mwuerms/lighthouse_hardware/scad/lighthouse/display.scad

/**
 * Martin Egli
 * 2024-05-15
 * testing honey comb structure to create the display
 * wall thickness: 0.5 mm
 * printing: 0.2 mm layer height
 */

use <hexagonparts.scad>
use <m3screw.scad>

hex_rad = 8/2;
/* calculate hexagon center positions
 * r: radius, use "hex_rad"
 * n: index in x axis
 * m: index in y axis
 * even columns
 * dxeven = n*2*r*cos(30)
 * dyeven = m*3/2*r
 * odd columns
 * dxodd = n*3/2*r
 * dyodd = (m-1/2)*r*cos(30)
 */
dx_even_factor = 3/2*hex_rad; // see dxeven = m*3*r
dy_even_factor = 2*hex_rad*cos(30); // see dyeven = n*2*r*cos(30)
dx_odd_factor = 3/2*hex_rad; // see dxodd = m*3/2*r
dy_odd_factor = hex_rad*cos(30); // see dyodd = (2n+1)*r*cos(30)

module display_m3_mount_cut() {
    place_m3_mount_cut(0, 2);
    place_m3_mount_cut(5, -2);
    place_m3_mount_cut(5, 6);
    place_m3_mount_cut(10, 5);
    place_m3_mount_cut(13, -2);
    place_m3_mount_cut(15, 6);
    place_m3_mount_cut(20, 4);
}

// - plain display ------------------
module plain_display_cover() {
    place_hexagon_cover_element(0, 0);
    place_hexagon_cover_element(0, 1);
    *place_hexagon_cover_element(0, 2);
    
    place_hexagon_cover_element(1, -1);
    place_hexagon_cover_element(1, 0);
    place_hexagon_cover_element(1, 1);
    place_hexagon_cover_element(1, 2);
    place_hexagon_cover_element(1, 3);
    place_hexagon_cover_element(1, 4);
    place_hexagon_cover_element(1, 5);

    place_hexagon_cover_element(2, -1);
    place_hexagon_cover_element(2, 0);
    place_hexagon_cover_element(2, 1);
    place_hexagon_cover_element(2, 2);
    place_hexagon_cover_element(2, 3);
    place_hexagon_cover_element(2, 4);
    place_hexagon_cover_element(2, 5);

    place_hexagon_cover_element(3, -1);
    place_hexagon_cover_element(3, 0);
    place_hexagon_cover_element(3, 1);
    place_hexagon_cover_element(3, 2);
    place_hexagon_cover_element(3, 3);
    place_hexagon_cover_element(3, 4);
    place_hexagon_cover_element(3, 5);
    place_hexagon_cover_element(3, 6);

    place_hexagon_cover_element(4, -2);
    place_hexagon_cover_element(4, -1);
    place_hexagon_cover_element(4, 0);
    place_hexagon_cover_element(4, 1);
    place_hexagon_cover_element(4, 2);
    place_hexagon_cover_element(4, 3);
    place_hexagon_cover_element(4, 4);
    place_hexagon_cover_element(4, 5);

    *place_hexagon_cover_element(5, -2);
    place_hexagon_cover_element(5, -1);
    place_hexagon_cover_element(5, 0);
    place_hexagon_cover_element(5, 1);
    place_hexagon_cover_element(5, 2);
    place_hexagon_cover_element(5, 3);
    place_hexagon_cover_element(5, 4);
    place_hexagon_cover_element(5, 5);

    place_hexagon_cover_element(6, -2);
    place_hexagon_cover_element(6, -1);
    place_hexagon_cover_element(6, 0);
    place_hexagon_cover_element(6, 1);
    place_hexagon_cover_element(6, 2);
    place_hexagon_cover_element(6, 3);
    place_hexagon_cover_element(6, 4);
    place_hexagon_cover_element(6, 5);

    place_hexagon_cover_element(7, -1);
    place_hexagon_cover_element(7, 0);
    place_hexagon_cover_element(7, 1);
    place_hexagon_cover_element(7, 2);
    place_hexagon_cover_element(7, 3);
    place_hexagon_cover_element(7, 4);
    place_hexagon_cover_element(7, 5);
    place_hexagon_cover_element(7, 6);

    place_hexagon_cover_element(8, -2);
    place_hexagon_cover_element(8, -1);
    place_hexagon_cover_element(8, 0);
    place_hexagon_cover_element(8, 1);
    place_hexagon_cover_element(8, 2);
    place_hexagon_cover_element(8, 3);
    place_hexagon_cover_element(8, 4);
    place_hexagon_cover_element(8, 5);

    place_hexagon_cover_element(9, -2);
    place_hexagon_cover_element(9, -1);
    place_hexagon_cover_element(9, 0);
    place_hexagon_cover_element(9, 1);
    place_hexagon_cover_element(9, 2);
    place_hexagon_cover_element(9, 3);
    place_hexagon_cover_element(9, 4);
    place_hexagon_cover_element(9, 5);

    place_hexagon_cover_element(10, -2);
    place_hexagon_cover_element(10, -1);
    place_hexagon_cover_element(10, 0);
    place_hexagon_cover_element(10, 1);
    place_hexagon_cover_element(10, 2);
    place_hexagon_cover_element(10, 3);
    place_hexagon_cover_element(10, 4);
    *place_hexagon_cover_element(10, 5);

    place_hexagon_cover_element(11, -1);
    place_hexagon_cover_element(11, 0);
    place_hexagon_cover_element(11, 1);
    place_hexagon_cover_element(11, 2);
    place_hexagon_cover_element(11, 3);
    place_hexagon_cover_element(11, 4);
    place_hexagon_cover_element(11, 5);

    place_hexagon_cover_element(12, -2);
    place_hexagon_cover_element(12, -1);
    place_hexagon_cover_element(12, 0);
    place_hexagon_cover_element(12, 1);
    place_hexagon_cover_element(12, 2);
    place_hexagon_cover_element(12, 3);
    place_hexagon_cover_element(12, 4);
    place_hexagon_cover_element(12, 5);

    *place_hexagon_cover_element(13, -2);
    place_hexagon_cover_element(13, -1);
    place_hexagon_cover_element(13, 0);
    place_hexagon_cover_element(13, 1);
    place_hexagon_cover_element(13, 2);
    place_hexagon_cover_element(13, 3);
    place_hexagon_cover_element(13, 4);
    place_hexagon_cover_element(13, 5);
    place_hexagon_cover_element(13, 6);

    place_hexagon_cover_element(14, -2);
    place_hexagon_cover_element(14, -1);
    place_hexagon_cover_element(14, 0);
    place_hexagon_cover_element(14, 1);
    place_hexagon_cover_element(14, 2);
    place_hexagon_cover_element(14, 3);
    place_hexagon_cover_element(14, 4);
    place_hexagon_cover_element(14, 5);

    place_hexagon_cover_element(15, -1);
    place_hexagon_cover_element(15, 0);
    place_hexagon_cover_element(15, 1);
    place_hexagon_cover_element(15, 2);
    place_hexagon_cover_element(15, 3);
    place_hexagon_cover_element(15, 4);
    place_hexagon_cover_element(15, 5);

    place_hexagon_cover_element(16, -2);
    place_hexagon_cover_element(16, -1);
    place_hexagon_cover_element(16, 0);
    place_hexagon_cover_element(16, 1);
    place_hexagon_cover_element(16, 2);
    place_hexagon_cover_element(16, 3);
    place_hexagon_cover_element(16, 4);
    place_hexagon_cover_element(16, 5);

    place_hexagon_cover_element(17, -1);
    place_hexagon_cover_element(17, 0);
    place_hexagon_cover_element(17, 1);
    place_hexagon_cover_element(17, 2);
    place_hexagon_cover_element(17, 3);
    place_hexagon_cover_element(17, 4);
    place_hexagon_cover_element(17, 5);
    place_hexagon_cover_element(17, 6);

    place_hexagon_cover_element(18, -1);
    place_hexagon_cover_element(18, 0);
    place_hexagon_cover_element(18, 1);
    place_hexagon_cover_element(18, 2);
    place_hexagon_cover_element(18, 3);
    place_hexagon_cover_element(18, 4);
    place_hexagon_cover_element(18, 5);

    place_hexagon_cover_element(19, 1);
    place_hexagon_cover_element(19, 2);
    place_hexagon_cover_element(19, 3);
    place_hexagon_cover_element(19, 4);
    place_hexagon_cover_element(19, 5);

    place_hexagon_cover_element(20, 2);
    place_hexagon_cover_element(20, 3);
    *place_hexagon_cover_element(20, 4);
    
    // mounts
    /*
    place_hexagon_cover_element_m3_mount(0, 2);
    place_hexagon_cover_element_m3_mount(5, -2);
    place_hexagon_cover_element_m3_mount(5, 6);
    place_hexagon_cover_element_m3_mount(10, 5);
    place_hexagon_cover_element_m3_mount(13, -2);
    place_hexagon_cover_element_m3_mount(15, 6);
    place_hexagon_cover_element_m3_mount(20, 4);
    */
    // no mounts
    place_hexagon_cover_element(0, 2);
    place_hexagon_cover_element(5, -2);
    place_hexagon_cover_element(5, 6);
    place_hexagon_cover_element(10, 5);
    place_hexagon_cover_element(13, -2);
    place_hexagon_cover_element(15, 6);
    place_hexagon_cover_element(20, 4);
}

module plain_display_cover_cut() {
    place_hexagon_cover_element_cut(0, 0);
    place_hexagon_cover_element_cut(0, 1);
    *place_hexagon_cover_element_cut(0, 2);
    
    place_hexagon_cover_element_cut(1, -1);
    place_hexagon_cover_element_cut(1, 0);
    place_hexagon_cover_element_cut(1, 1);
    place_hexagon_cover_element_cut(1, 2);
    place_hexagon_cover_element_cut(1, 3);
    place_hexagon_cover_element_cut(1, 4);
    place_hexagon_cover_element_cut(1, 5);

    place_hexagon_cover_element_cut(2, -1);
    place_hexagon_cover_element_cut(2, 0);
    place_hexagon_cover_element_cut(2, 1);
    place_hexagon_cover_element_cut(2, 2);
    place_hexagon_cover_element_cut(2, 3);
    place_hexagon_cover_element_cut(2, 4);
    place_hexagon_cover_element_cut(2, 5);

    place_hexagon_cover_element_cut(3, -1);
    place_hexagon_cover_element_cut(3, 0);
    place_hexagon_cover_element_cut(3, 1);
    place_hexagon_cover_element_cut(3, 2);
    place_hexagon_cover_element_cut(3, 3);
    place_hexagon_cover_element_cut(3, 4);
    place_hexagon_cover_element_cut(3, 5);
    place_hexagon_cover_element_cut(3, 6);

    place_hexagon_cover_element_cut(4, -2);
    place_hexagon_cover_element_cut(4, -1);
    place_hexagon_cover_element_cut(4, 0);
    place_hexagon_cover_element_cut(4, 1);
    place_hexagon_cover_element_cut(4, 2);
    place_hexagon_cover_element_cut(4, 3);
    place_hexagon_cover_element_cut(4, 4);
    place_hexagon_cover_element_cut(4, 5);

    *place_hexagon_cover_element_cut(5, -2);
    place_hexagon_cover_element_cut(5, -1);
    place_hexagon_cover_element_cut(5, 0);
    place_hexagon_cover_element_cut(5, 1);
    place_hexagon_cover_element_cut(5, 2);
    place_hexagon_cover_element_cut(5, 3);
    place_hexagon_cover_element_cut(5, 4);
    place_hexagon_cover_element_cut(5, 5);

    place_hexagon_cover_element_cut(6, -2);
    place_hexagon_cover_element_cut(6, -1);
    place_hexagon_cover_element_cut(6, 0);
    place_hexagon_cover_element_cut(6, 1);
    place_hexagon_cover_element_cut(6, 2);
    place_hexagon_cover_element_cut(6, 3);
    place_hexagon_cover_element_cut(6, 4);
    place_hexagon_cover_element_cut(6, 5);

    place_hexagon_cover_element_cut(7, -1);
    place_hexagon_cover_element_cut(7, 0);
    place_hexagon_cover_element_cut(7, 1);
    place_hexagon_cover_element_cut(7, 2);
    place_hexagon_cover_element_cut(7, 3);
    place_hexagon_cover_element_cut(7, 4);
    place_hexagon_cover_element_cut(7, 5);
    place_hexagon_cover_element_cut(7, 6);

    place_hexagon_cover_element_cut(8, -2);
    place_hexagon_cover_element_cut(8, -1);
    place_hexagon_cover_element_cut(8, 0);
    place_hexagon_cover_element_cut(8, 1);
    place_hexagon_cover_element_cut(8, 2);
    place_hexagon_cover_element_cut(8, 3);
    place_hexagon_cover_element_cut(8, 4);
    place_hexagon_cover_element_cut(8, 5);

    place_hexagon_cover_element_cut(9, -2);
    place_hexagon_cover_element_cut(9, -1);
    place_hexagon_cover_element_cut(9, 0);
    place_hexagon_cover_element_cut(9, 1);
    place_hexagon_cover_element_cut(9, 2);
    place_hexagon_cover_element_cut(9, 3);
    place_hexagon_cover_element_cut(9, 4);
    place_hexagon_cover_element_cut(9, 5);

    place_hexagon_cover_element_cut(10, -2);
    place_hexagon_cover_element_cut(10, -1);
    place_hexagon_cover_element_cut(10, 0);
    place_hexagon_cover_element_cut(10, 1);
    place_hexagon_cover_element_cut(10, 2);
    place_hexagon_cover_element_cut(10, 3);
    place_hexagon_cover_element_cut(10, 4);
    *place_hexagon_cover_element_cut(10, 5);

    place_hexagon_cover_element_cut(11, -1);
    place_hexagon_cover_element_cut(11, 0);
    place_hexagon_cover_element_cut(11, 1);
    place_hexagon_cover_element_cut(11, 2);
    place_hexagon_cover_element_cut(11, 3);
    place_hexagon_cover_element_cut(11, 4);
    place_hexagon_cover_element_cut(11, 5);

    place_hexagon_cover_element_cut(12, -2);
    place_hexagon_cover_element_cut(12, -1);
    place_hexagon_cover_element_cut(12, 0);
    place_hexagon_cover_element_cut(12, 1);
    place_hexagon_cover_element_cut(12, 2);
    place_hexagon_cover_element_cut(12, 3);
    place_hexagon_cover_element_cut(12, 4);
    place_hexagon_cover_element_cut(12, 5);

    *place_hexagon_cover_element_cut(13, -2);
    place_hexagon_cover_element_cut(13, -1);
    place_hexagon_cover_element_cut(13, 0);
    place_hexagon_cover_element_cut(13, 1);
    place_hexagon_cover_element_cut(13, 2);
    place_hexagon_cover_element_cut(13, 3);
    place_hexagon_cover_element_cut(13, 4);
    place_hexagon_cover_element_cut(13, 5);
    place_hexagon_cover_element_cut(13, 6);

    place_hexagon_cover_element_cut(14, -2);
    place_hexagon_cover_element_cut(14, -1);
    place_hexagon_cover_element_cut(14, 0);
    place_hexagon_cover_element_cut(14, 1);
    place_hexagon_cover_element_cut(14, 2);
    place_hexagon_cover_element_cut(14, 3);
    place_hexagon_cover_element_cut(14, 4);
    place_hexagon_cover_element_cut(14, 5);

    place_hexagon_cover_element_cut(15, -1);
    place_hexagon_cover_element_cut(15, 0);
    place_hexagon_cover_element_cut(15, 1);
    place_hexagon_cover_element_cut(15, 2);
    place_hexagon_cover_element_cut(15, 3);
    place_hexagon_cover_element_cut(15, 4);
    place_hexagon_cover_element_cut(15, 5);

    place_hexagon_cover_element_cut(16, -2);
    place_hexagon_cover_element_cut(16, -1);
    place_hexagon_cover_element_cut(16, 0);
    place_hexagon_cover_element_cut(16, 1);
    place_hexagon_cover_element_cut(16, 2);
    place_hexagon_cover_element_cut(16, 3);
    place_hexagon_cover_element_cut(16, 4);
    place_hexagon_cover_element_cut(16, 5);

    place_hexagon_cover_element_cut(17, -1);
    place_hexagon_cover_element_cut(17, 0);
    place_hexagon_cover_element_cut(17, 1);
    place_hexagon_cover_element_cut(17, 2);
    place_hexagon_cover_element_cut(17, 3);
    place_hexagon_cover_element_cut(17, 4);
    place_hexagon_cover_element_cut(17, 5);
    place_hexagon_cover_element_cut(17, 6);

    place_hexagon_cover_element_cut(18, -1);
    place_hexagon_cover_element_cut(18, 0);
    place_hexagon_cover_element_cut(18, 1);
    place_hexagon_cover_element_cut(18, 2);
    place_hexagon_cover_element_cut(18, 3);
    place_hexagon_cover_element_cut(18, 4);
    place_hexagon_cover_element_cut(18, 5);

    place_hexagon_cover_element_cut(19, 1);
    place_hexagon_cover_element_cut(19, 2);
    place_hexagon_cover_element_cut(19, 3);
    place_hexagon_cover_element_cut(19, 4);
    place_hexagon_cover_element_cut(19, 5);

    place_hexagon_cover_element_cut(20, 2);
    place_hexagon_cover_element_cut(20, 3);
    *place_hexagon_cover_element_cut(20, 4);
    
    // mounts
    place_hexagon_cover_element_m3_mount_cut(0, 2);
    place_hexagon_cover_element_m3_mount_cut(5, -2);
    place_hexagon_cover_element_m3_mount_cut(5, 6);
    place_hexagon_cover_element_m3_mount_cut(10, 5);
    place_hexagon_cover_element_m3_mount_cut(13, -2);
    place_hexagon_cover_element_m3_mount_cut(15, 6);
    place_hexagon_cover_element_m3_mount_cut(20, 4);
}

// - display ------------------
// red leds: 8*4 + 4*5 + 2 + 7 = 61
// control individualy
module display_clock_cover() {
    place_hexagon_cover_element(0, 0);
    place_hexagon_cover_element(0, 1);
    *place_hexagon_cover_element(0, 2);
    
    place_hexagon_cover_element(1, -1);
    place_hexagon_cover_element(1, 0);
    place_hexagon_cover_element(1, 1);
    place_hexagon_cover_element(1, 2);
    place_hexagon_cover_element(1, 3);
    place_hexagon_cover_element(1, 4);
    place_hexagon_cover_element(1, 5);

    place_hexagon_cover_element(2, -1);
    place_hexagon_cover_element(2, 0);
    place_hexagon_cover_element_led(2, 1);
    place_hexagon_cover_element_led(2, 2);
    place_hexagon_cover_element_led(2, 3);
    place_hexagon_cover_element_led(2, 4);
    place_hexagon_cover_element(2, 5);

    place_hexagon_cover_element(3, -1);
    place_hexagon_cover_element(3, 0);
    place_hexagon_cover_element_led(3, 1);
    place_hexagon_cover_element_led(3, 2);
    place_hexagon_cover_element_led(3, 3);
    place_hexagon_cover_element_led(3, 4);
    place_hexagon_cover_element_led(3, 5);
    place_hexagon_cover_element(3, 6);

    place_hexagon_cover_element(4, -2);
    place_hexagon_cover_element_led(4, -1);
    place_hexagon_cover_element(4, 0);
    place_hexagon_cover_element_led(4, 1);
    place_hexagon_cover_element_led(4, 2);
    place_hexagon_cover_element_led(4, 3);
    place_hexagon_cover_element_led(4, 4);
    place_hexagon_cover_element(4, 5);

    *place_hexagon_cover_element(5, -2);
    place_hexagon_cover_element(5, -1);
    place_hexagon_cover_element(5, 0);
    place_hexagon_cover_element(5, 1);
    place_hexagon_cover_element(5, 2);
    place_hexagon_cover_element(5, 3);
    place_hexagon_cover_element(5, 4);
    place_hexagon_cover_element(5, 5);

    place_hexagon_cover_element(6, -2);
    place_hexagon_cover_element_led(6, -1);
    place_hexagon_cover_element(6, 0);
    place_hexagon_cover_element_led(6, 1);
    place_hexagon_cover_element_led(6, 2);
    place_hexagon_cover_element_led(6, 3);
    place_hexagon_cover_element_led(6, 4);
    place_hexagon_cover_element(6, 5);

    place_hexagon_cover_element(7, -1);
    place_hexagon_cover_element(7, 0);
    place_hexagon_cover_element_led(7, 1);
    place_hexagon_cover_element_led(7, 2);
    place_hexagon_cover_element_led(7, 3);
    place_hexagon_cover_element_led(7, 4);
    place_hexagon_cover_element_led(7, 5);
    place_hexagon_cover_element(7, 6);

    place_hexagon_cover_element(8, -2);
    place_hexagon_cover_element_led(8, -1);
    place_hexagon_cover_element(8, 0);
    place_hexagon_cover_element_led(8, 1);
    place_hexagon_cover_element_led(8, 2);
    place_hexagon_cover_element_led(8, 3);
    place_hexagon_cover_element_led(8, 4);
    place_hexagon_cover_element(8, 5);

    place_hexagon_cover_element(9, -2);
    place_hexagon_cover_element(9, -1);
    place_hexagon_cover_element(9, 0);
    place_hexagon_cover_element(9, 1);
    place_hexagon_cover_element(9, 2);
    place_hexagon_cover_element(9, 3);
    place_hexagon_cover_element(9, 4);
    place_hexagon_cover_element(9, 5);

    place_hexagon_cover_element(10, -2);
    place_hexagon_cover_element_led(10, -1);
    place_hexagon_cover_element(10, 0);
    place_hexagon_cover_element_led(10, 1);
    place_hexagon_cover_element(10, 2);
    place_hexagon_cover_element_led(10, 3);
    place_hexagon_cover_element(10, 4);
    *place_hexagon_cover_element(10, 5);

    place_hexagon_cover_element(11, -1);
    place_hexagon_cover_element(11, 0);
    place_hexagon_cover_element(11, 1);
    place_hexagon_cover_element(11, 2);
    place_hexagon_cover_element(11, 3);
    place_hexagon_cover_element(11, 4);
    place_hexagon_cover_element(11, 5);

    place_hexagon_cover_element(12, -2);
    place_hexagon_cover_element_led(12, -1);
    place_hexagon_cover_element(12, 0);
    place_hexagon_cover_element_led(12, 1);
    place_hexagon_cover_element_led(12, 2);
    place_hexagon_cover_element_led(12, 3);
    place_hexagon_cover_element_led(12, 4);
    place_hexagon_cover_element(12, 5);

    *place_hexagon_cover_element(13, -2);
    place_hexagon_cover_element(13, -1);
    place_hexagon_cover_element(13, 0);
    place_hexagon_cover_element_led(13, 1);
    place_hexagon_cover_element_led(13, 2);
    place_hexagon_cover_element_led(13, 3);
    place_hexagon_cover_element_led(13, 4);
    place_hexagon_cover_element_led(13, 5);
    place_hexagon_cover_element(13, 6);

    place_hexagon_cover_element(14, -2);
    place_hexagon_cover_element_led(14, -1);
    place_hexagon_cover_element(14, 0);
    place_hexagon_cover_element_led(14, 1);
    place_hexagon_cover_element_led(14, 2);
    place_hexagon_cover_element_led(14, 3);
    place_hexagon_cover_element_led(14, 4);
    place_hexagon_cover_element(14, 5);

    place_hexagon_cover_element(15, -1);
    place_hexagon_cover_element(15, 0);
    place_hexagon_cover_element(15, 1);
    place_hexagon_cover_element(15, 2);
    place_hexagon_cover_element(15, 3);
    place_hexagon_cover_element(15, 4);
    place_hexagon_cover_element(15, 5);

    place_hexagon_cover_element(16, -2);
    place_hexagon_cover_element_led(16, -1);
    place_hexagon_cover_element(16, 0);
    place_hexagon_cover_element_led(16, 1);
    place_hexagon_cover_element_led(16, 2);
    place_hexagon_cover_element_led(16, 3);
    place_hexagon_cover_element_led(16, 4);
    place_hexagon_cover_element(16, 5);

    place_hexagon_cover_element(17, -1);
    place_hexagon_cover_element(17, 0);
    place_hexagon_cover_element_led(17, 1);
    place_hexagon_cover_element_led(17, 2);
    place_hexagon_cover_element_led(17, 3);
    place_hexagon_cover_element_led(17, 4);
    place_hexagon_cover_element_led(17, 5);
    place_hexagon_cover_element(17, 6);

    place_hexagon_cover_element(18, -1);
    place_hexagon_cover_element(18, 0);
    place_hexagon_cover_element_led(18, 1);
    place_hexagon_cover_element_led(18, 2);
    place_hexagon_cover_element_led(18, 3);
    place_hexagon_cover_element_led(18, 4);
    place_hexagon_cover_element(18, 5);

    place_hexagon_cover_element(19, 1);
    place_hexagon_cover_element(19, 2);
    place_hexagon_cover_element(19, 3);
    place_hexagon_cover_element(19, 4);
    place_hexagon_cover_element(19, 5);

    place_hexagon_cover_element(20, 2);
    place_hexagon_cover_element(20, 3);
    place_hexagon_cover_element(20, 4);
    
    // mounts
    /*
    place_hexagon_cover_element_m3_mount(0, 2);
    place_hexagon_cover_element_m3_mount(5, -2);
    place_hexagon_cover_element_m3_mount(5, 6);
    place_hexagon_cover_element_m3_mount(10, 5);
    place_hexagon_cover_element_m3_mount(13, -2);
    place_hexagon_cover_element_m3_mount(15, 6);
    place_hexagon_cover_element_m3_mount(20, 4);
    */
    // no mounts
    place_hexagon_cover_element(0, 2);
    place_hexagon_cover_element(5, -2);
    place_hexagon_cover_element(5, 6);
    place_hexagon_cover_element(10, 5);
    place_hexagon_cover_element(13, -2);
    place_hexagon_cover_element(15, 6);
    place_hexagon_cover_element(20, 4);
}

// - display ------------------
// red leds: 8*4 + 4*5 + 2 + 7 = 61
// control individualy
// white leds: 37 -> use only 36
// control together
module display_backlight_cover() {
    place_hexagon_cover_element(0, 0);
    place_hexagon_cover_element(0, 1);
    *place_hexagon_cover_element(0, 2);
    
    place_hexagon_cover_element(1, -1);
    place_hexagon_cover_element(1, 0);
    place_hexagon_cover_element_led(1, 1, "white");
    place_hexagon_cover_element_led(1, 2, "white");
    place_hexagon_cover_element(1, 3);
    place_hexagon_cover_element(1, 4);
    place_hexagon_cover_element(1, 5);

    place_hexagon_cover_element(2, -1);
    place_hexagon_cover_element_led(2, 0, "white");
    place_hexagon_cover_element_led(2, 1);
    place_hexagon_cover_element_led(2, 2);
    place_hexagon_cover_element_led(2, 3);
    place_hexagon_cover_element_led(2, 4);
    place_hexagon_cover_element(2, 5);

    place_hexagon_cover_element(3, -1);
    place_hexagon_cover_element_led(3, 0, "white");
    place_hexagon_cover_element_led(3, 1);
    place_hexagon_cover_element_led(3, 2);
    place_hexagon_cover_element_led(3, 3);
    place_hexagon_cover_element_led(3, 4);
    place_hexagon_cover_element_led(3, 5);
    place_hexagon_cover_element(3, 6);

    place_hexagon_cover_element(4, -2);
    place_hexagon_cover_element_led(4, -1);
    place_hexagon_cover_element_led(4, 0, "white");
    place_hexagon_cover_element_led(4, 1);
    place_hexagon_cover_element_led(4, 2);
    place_hexagon_cover_element_led(4, 3);
    place_hexagon_cover_element_led(4, 4);
    place_hexagon_cover_element(4, 5);

    *place_hexagon_cover_element(5, -2);
    place_hexagon_cover_element(5, -1);
    place_hexagon_cover_element_led(5, 0, "white");
    place_hexagon_cover_element_led(5, 1, "white");
    place_hexagon_cover_element_led(5, 2, "white");
    place_hexagon_cover_element_led(5, 3, "white");
    place_hexagon_cover_element_led(5, 4, "white");
    place_hexagon_cover_element(5, 5);

    place_hexagon_cover_element(6, -2);
    place_hexagon_cover_element_led(6, -1);
    place_hexagon_cover_element_led(6, 0, "white");
    place_hexagon_cover_element_led(6, 1);
    place_hexagon_cover_element_led(6, 2);
    place_hexagon_cover_element_led(6, 3);
    place_hexagon_cover_element_led(6, 4);
    place_hexagon_cover_element(6, 5);

    place_hexagon_cover_element(7, -1);
    place_hexagon_cover_element_led(7, 0, "white");
    place_hexagon_cover_element_led(7, 1);
    place_hexagon_cover_element_led(7, 2);
    place_hexagon_cover_element_led(7, 3);
    place_hexagon_cover_element_led(7, 4);
    place_hexagon_cover_element_led(7, 5);
    place_hexagon_cover_element(7, 6);

    place_hexagon_cover_element(8, -2);
    place_hexagon_cover_element_led(8, -1);
    place_hexagon_cover_element_led(8, 0, "white");
    place_hexagon_cover_element_led(8, 1);
    place_hexagon_cover_element_led(8, 2);
    place_hexagon_cover_element_led(8, 3);
    place_hexagon_cover_element_led(8, 4);
    place_hexagon_cover_element(8, 5);

    place_hexagon_cover_element(9, -2);
    place_hexagon_cover_element_led(9, -1, "white");
    place_hexagon_cover_element_led(9, 0, "white");
    place_hexagon_cover_element_led(9, 1, "white");
    place_hexagon_cover_element_led(9, 2, "white");
    place_hexagon_cover_element_led(9, 3, "white");
    place_hexagon_cover_element_led(9, 4, "white");
    place_hexagon_cover_element(9, 5);

    place_hexagon_cover_element(10, -2);
    place_hexagon_cover_element_led(10, -1);
    place_hexagon_cover_element_led(10, 0, "white");
    place_hexagon_cover_element_led(10, 1);
    place_hexagon_cover_element_led(10, 2, "white");
    place_hexagon_cover_element_led(10, 3);
    place_hexagon_cover_element(10, 4);
    *place_hexagon_cover_element(10, 5);

    place_hexagon_cover_element(11, -1);
    place_hexagon_cover_element_led(11, 0, "white");
    place_hexagon_cover_element_led(11, 1, "white");
    place_hexagon_cover_element_led(11, 2, "white");
    place_hexagon_cover_element_led(11, 3, "white");
    place_hexagon_cover_element_led(11, 4, "white");
    place_hexagon_cover_element(11, 5);

    place_hexagon_cover_element(12, -2);
    place_hexagon_cover_element_led(12, -1);
    place_hexagon_cover_element_led(12, 0, "white");
    place_hexagon_cover_element_led(12, 1);
    place_hexagon_cover_element_led(12, 2);
    place_hexagon_cover_element_led(12, 3);
    place_hexagon_cover_element_led(12, 4);
    place_hexagon_cover_element(12, 5);

    *place_hexagon_cover_element(13, -2);
    place_hexagon_cover_element(13, -1);
    place_hexagon_cover_element_led(13, 0, "white");
    place_hexagon_cover_element_led(13, 1);
    place_hexagon_cover_element_led(13, 2);
    place_hexagon_cover_element_led(13, 3);
    place_hexagon_cover_element_led(13, 4);
    place_hexagon_cover_element_led(13, 5);
    place_hexagon_cover_element(13, 6);

    place_hexagon_cover_element(14, -2);
    place_hexagon_cover_element_led(14, -1);
    place_hexagon_cover_element_led(14, 0, "white");
    place_hexagon_cover_element_led(14, 1);
    place_hexagon_cover_element_led(14, 2);
    place_hexagon_cover_element_led(14, 3);
    place_hexagon_cover_element_led(14, 4);
    place_hexagon_cover_element(14, 5);

    place_hexagon_cover_element(15, -1);
    place_hexagon_cover_element_led(15, 0, "white");
    place_hexagon_cover_element_led(15, 1, "white");
    place_hexagon_cover_element_led(15, 2, "white");
    place_hexagon_cover_element_led(15, 3, "white");
    place_hexagon_cover_element_led(15, 4, "white");
    place_hexagon_cover_element(15, 5);

    place_hexagon_cover_element(16, -2);
    place_hexagon_cover_element_led(16, -1);
    place_hexagon_cover_element_led(16, 0, "white");
    place_hexagon_cover_element_led(16, 1);
    place_hexagon_cover_element_led(16, 2);
    place_hexagon_cover_element_led(16, 3);
    place_hexagon_cover_element_led(16, 4);
    place_hexagon_cover_element(16, 5);

    place_hexagon_cover_element(17, -1);
    place_hexagon_cover_element_led(17, 0, "white");
    place_hexagon_cover_element_led(17, 1);
    place_hexagon_cover_element_led(17, 2);
    place_hexagon_cover_element_led(17, 3);
    place_hexagon_cover_element_led(17, 4);
    place_hexagon_cover_element_led(17, 5);
    place_hexagon_cover_element(17, 6);

    place_hexagon_cover_element(18, -1);
    place_hexagon_cover_element(18, 0);
    place_hexagon_cover_element_led(18, 1);
    place_hexagon_cover_element_led(18, 2);
    place_hexagon_cover_element_led(18, 3);
    place_hexagon_cover_element_led(18, 4);
    place_hexagon_cover_element(18, 5);

    place_hexagon_cover_element(19, 1);
    place_hexagon_cover_element(19, 2);
    place_hexagon_cover_element_led(19, 3, "white");
    place_hexagon_cover_element_led(19, 4, "white");
    place_hexagon_cover_element(19, 5);

    place_hexagon_cover_element(20, 2);
    place_hexagon_cover_element(20, 3);
    place_hexagon_cover_element(20, 4);
    
    // mounts
    /*
    place_hexagon_cover_element_m3_mount(0, 2);
    place_hexagon_cover_element_m3_mount(5, -2);
    place_hexagon_cover_element_m3_mount(5, 6);
    place_hexagon_cover_element_m3_mount(10, 5);
    place_hexagon_cover_element_m3_mount(13, -2);
    place_hexagon_cover_element_m3_mount(15, 6);
    place_hexagon_cover_element_m3_mount(20, 4);
    */
    // no mounts
    place_hexagon_cover_element(0, 2);
    place_hexagon_cover_element(5, -2);
    place_hexagon_cover_element(5, 6);
    place_hexagon_cover_element(10, 5);
    place_hexagon_cover_element(13, -2);
    place_hexagon_cover_element(15, 6);
    place_hexagon_cover_element(20, 4);
}


// - spacer ---------------------------
module led_spacer(mark_center = 1) {
    place_hexagon_spacer_element(1, 1, mark_center = mark_center);
    place_hexagon_spacer_element(1, 2, mark_center = mark_center);
    place_hexagon_spacer_element(1, 3, mark_center = mark_center);
    
    place_hexagon_spacer_element(2, 0, mark_center = mark_center);
    place_hexagon_spacer_element(2, 1, mark_center = mark_center);
    place_hexagon_spacer_element(2, 2, mark_center = mark_center);
    place_hexagon_spacer_element(2, 3, mark_center = mark_center);
    place_hexagon_spacer_element(2, 4, mark_center = mark_center);
    
    place_hexagon_spacer_element(3, 0, mark_center = mark_center);
    place_hexagon_spacer_element(3, 1, mark_center = mark_center);
    place_hexagon_spacer_element(3, 2, mark_center = mark_center);
    place_hexagon_spacer_element(3, 3, mark_center = mark_center);
    place_hexagon_spacer_element(3, 4, mark_center = mark_center);
    place_hexagon_spacer_element(3, 5, mark_center = mark_center);
    
    place_hexagon_spacer_element(4, -1, mark_center = mark_center);
    place_hexagon_spacer_element(4, 0, mark_center = mark_center);
    place_hexagon_spacer_element(4, 1, mark_center = mark_center);
    place_hexagon_spacer_element(4, 2, mark_center = mark_center);
    place_hexagon_spacer_element(4, 3, mark_center = mark_center);
    place_hexagon_spacer_element(4, 4, mark_center = mark_center);
    
    place_hexagon_spacer_element(5, -1, mark_center = mark_center);
    place_hexagon_spacer_element(5, 0, mark_center = mark_center);
    place_hexagon_spacer_element(5, 1, mark_center = mark_center);
    place_hexagon_spacer_element(5, 2, mark_center = mark_center);
    place_hexagon_spacer_element(5, 3, mark_center = mark_center);
    place_hexagon_spacer_element(5, 4, mark_center = mark_center);
    place_hexagon_spacer_element(5, 5, mark_center = mark_center);
    
    place_hexagon_spacer_element(6, -1, mark_center = mark_center);
    place_hexagon_spacer_element(6, 0, mark_center = mark_center);
    place_hexagon_spacer_element(6, 1, mark_center = mark_center);
    place_hexagon_spacer_element(6, 2, mark_center = mark_center);
    place_hexagon_spacer_element(6, 3, mark_center = mark_center);
    place_hexagon_spacer_element(6, 4, mark_center = mark_center);

    place_hexagon_spacer_element(7, 0, mark_center = mark_center);
    place_hexagon_spacer_element(7, 1, mark_center = mark_center);
    place_hexagon_spacer_element(7, 2, mark_center = mark_center);
    place_hexagon_spacer_element(7, 3, mark_center = mark_center);
    place_hexagon_spacer_element(7, 4, mark_center = mark_center);
    place_hexagon_spacer_element(7, 5, mark_center = mark_center);

    place_hexagon_spacer_element(8, -1, mark_center = mark_center);
    place_hexagon_spacer_element(8, 0, mark_center = mark_center);
    place_hexagon_spacer_element(8, 1, mark_center = mark_center);
    place_hexagon_spacer_element(8, 2, mark_center = mark_center);
    place_hexagon_spacer_element(8, 3, mark_center = mark_center);
    place_hexagon_spacer_element(8, 4, mark_center = mark_center);

    place_hexagon_spacer_element(9, -1, mark_center = mark_center);
    place_hexagon_spacer_element(9, 0, mark_center = mark_center);
    place_hexagon_spacer_element(9, 1, mark_center = mark_center);
    place_hexagon_spacer_element(9, 2, mark_center = mark_center);
    place_hexagon_spacer_element(9, 3, mark_center = mark_center);
    place_hexagon_spacer_element(9, 4, mark_center = mark_center);

    place_hexagon_spacer_element(10, -1, mark_center = mark_center);
    place_hexagon_spacer_element(10, 0, mark_center = mark_center);
    place_hexagon_spacer_element(10, 1, mark_center = mark_center);
    place_hexagon_spacer_element(10, 2, mark_center = mark_center);
    place_hexagon_spacer_element(10, 3, mark_center = mark_center);
    place_hexagon_spacer_element(10, 4, mark_center = mark_center);

    place_hexagon_spacer_element(11, 0, mark_center = mark_center);
    place_hexagon_spacer_element(11, 1, mark_center = mark_center);
    place_hexagon_spacer_element(11, 2, mark_center = mark_center);
    place_hexagon_spacer_element(11, 3, mark_center = mark_center);
    place_hexagon_spacer_element(11, 4, mark_center = mark_center);

    place_hexagon_spacer_element(12, -1, mark_center = mark_center);
    place_hexagon_spacer_element(12, 0, mark_center = mark_center);
    place_hexagon_spacer_element(12, 1, mark_center = mark_center);
    place_hexagon_spacer_element(12, 2, mark_center = mark_center);
    place_hexagon_spacer_element(12, 3, mark_center = mark_center);
    place_hexagon_spacer_element(12, 4, mark_center = mark_center);

    place_hexagon_spacer_element(13, -1, mark_center = mark_center);
    place_hexagon_spacer_element(13, 0, mark_center = mark_center);
    place_hexagon_spacer_element(13, 1, mark_center = mark_center);
    place_hexagon_spacer_element(13, 2, mark_center = mark_center);
    place_hexagon_spacer_element(13, 3, mark_center = mark_center);
    place_hexagon_spacer_element(13, 4, mark_center = mark_center);
    place_hexagon_spacer_element(13, 5, mark_center = mark_center);

    place_hexagon_spacer_element(14, -1, mark_center = mark_center);
    place_hexagon_spacer_element(14, 0, mark_center = mark_center);
    place_hexagon_spacer_element(14, 1, mark_center = mark_center);
    place_hexagon_spacer_element(14, 2, mark_center = mark_center);
    place_hexagon_spacer_element(14, 3, mark_center = mark_center);
    place_hexagon_spacer_element(14, 4, mark_center = mark_center);

    place_hexagon_spacer_element(15, 0, mark_center = mark_center);
    place_hexagon_spacer_element(15, 1, mark_center = mark_center);
    place_hexagon_spacer_element(15, 2, mark_center = mark_center);
    place_hexagon_spacer_element(15, 3, mark_center = mark_center);
    place_hexagon_spacer_element(15, 4, mark_center = mark_center);
    place_hexagon_spacer_element(15, 5, mark_center = mark_center);

    place_hexagon_spacer_element(16, -1, mark_center = mark_center);
    place_hexagon_spacer_element(16, 0, mark_center = mark_center);
    place_hexagon_spacer_element(16, 1, mark_center = mark_center);
    place_hexagon_spacer_element(16, 2, mark_center = mark_center);
    place_hexagon_spacer_element(16, 3, mark_center = mark_center);
    place_hexagon_spacer_element(16, 4, mark_center = mark_center);

    place_hexagon_spacer_element(17, 0, mark_center = mark_center);
    place_hexagon_spacer_element(17, 1, mark_center = mark_center);
    place_hexagon_spacer_element(17, 2, mark_center = mark_center);
    place_hexagon_spacer_element(17, 3, mark_center = mark_center);
    place_hexagon_spacer_element(17, 4, mark_center = mark_center);
    place_hexagon_spacer_element(17, 5, mark_center = mark_center);

    place_hexagon_spacer_element(18, 1, mark_center = mark_center);
    place_hexagon_spacer_element(18, 2, mark_center = mark_center);
    place_hexagon_spacer_element(18, 3, mark_center = mark_center);
    place_hexagon_spacer_element(18, 4, mark_center = mark_center);

    place_hexagon_spacer_element(19, 3, mark_center = mark_center);
    place_hexagon_spacer_element(19, 4, mark_center = mark_center);
    place_hexagon_spacer_element(19, 5, mark_center = mark_center);
    
    // mounts
    place_hexagon_spacer_element_m3_mount(0, 2);
    place_hexagon_spacer_element_m3_mount(5, -2);
    place_hexagon_spacer_element_m3_mount(5, 6);
    place_hexagon_spacer_element_m3_mount(10, 5);
    place_hexagon_spacer_element_m3_mount(13, -2);
    place_hexagon_spacer_element_m3_mount(15, 6);
    place_hexagon_spacer_element_m3_mount(20, 4);
}

module place_plain_display_cover(x_pos = 0, y_pos = 0) {
    if((x_pos % 2) == 0) {
        // even column
        translate([x_pos*dx_even_factor, y_pos*dy_even_factor, 0])
        plain_display_cover();
    }
    else {
        // odd column
        translate([x_pos*dx_odd_factor, (2*y_pos-1)*dy_odd_factor, 0])
        plain_display_cover();
    }
}

module place_plain_display_cover_cut(x_pos = 0, y_pos = 0) {
    if((x_pos % 2) == 0) {
        // even column
        translate([x_pos*dx_even_factor, y_pos*dy_even_factor, 0])
        plain_display_cover_cut();
    }
    else {
        // odd column
        translate([x_pos*dx_odd_factor, (2*y_pos-1)*dy_odd_factor, 0])
        plain_display_cover_cut();
    }
}

module place_display_m3_mount_cut(x_pos = 0, y_pos = 0) {
    if((x_pos % 2) == 0) {
        // even column
        translate([x_pos*dx_even_factor, y_pos*dy_even_factor, 0])
        display_m3_mount_cut();
    }
    else {
        // odd column
        translate([x_pos*dx_odd_factor, (2*y_pos-1)*dy_odd_factor, 0])
        display_m3_mount_cut();
    }
}

module place_display_clock_cover(x_pos = 0, y_pos = 0) {
    if((x_pos % 2) == 0) {
        // even column
        translate([x_pos*dx_even_factor, y_pos*dy_even_factor, 0])
        display_clock_cover();
    }
    else {
        // odd column
        translate([x_pos*dx_odd_factor, (2*y_pos-1)*dy_odd_factor, 0])
        display_clock_cover();
    }
}

module place_display_backlight_cover(x_pos = 0, y_pos = 0) {
    if((x_pos % 2) == 0) {
        // even column
        translate([x_pos*dx_even_factor, y_pos*dy_even_factor, 0])
        display_backlight_cover();
    }
    else {
        // odd column
        translate([x_pos*dx_odd_factor, (2*y_pos-1)*dy_odd_factor, 0])
        display_backlight_cover();
    }
}

module place_led_spacer(x_pos = 0, y_pos = 0) {
    if((x_pos % 2) == 0) {
        // even column
        translate([x_pos*dx_even_factor, y_pos*dy_even_factor, 0])
        led_spacer(mark_center = 0);
    }
    else {
        // odd column
        translate([x_pos*dx_odd_factor, (2*y_pos-1)*dy_odd_factor, 0])
        led_spacer(mark_center = 0);
    }
}

module place_led_spacer_mark_center(x_pos = 0, y_pos = 0) {
    if((x_pos % 2) == 0) {
        // even column
        translate([x_pos*dx_even_factor, y_pos*dy_even_factor, 0])
        led_spacer(mark_center = 1);
    }
    else {
        // odd column
        translate([x_pos*dx_odd_factor, (2*y_pos-1)*dy_odd_factor, 0])
        led_spacer(mark_center = 1);
    }
}

module led_spacer_mount_element() {
    difference() {
        place_hexagon_spacer_element_filled(0, 0);
        translate([0, 0, 5])
        pfla_m3_1_insert_cut();
    }
    translate([0, 0, 4.6])
    cylinder(d = 5, h = 0.4, $fn = 32);
    translate([0, 0, 5])
    cylinder(d = 2.8, h = 0.2, $fn = 32);
}

module place_led_spacer_mount_element(x_pos = 0, y_pos = 0) {
    if((x_pos % 2) == 0) {
        // even column
        translate([x_pos*dx_even_factor, y_pos*dy_even_factor, 0])
        led_spacer_mount_element();
    }
    else {
        // odd column
        translate([x_pos*dx_odd_factor, (2*y_pos-1)*dy_odd_factor, 0])
        led_spacer_mount_element();
    }
}

module led_spacer_mount() {
    // mounts
    place_led_spacer_mount_element(0, 2);
    place_led_spacer_mount_element(5, -2);
    place_led_spacer_mount_element(5, 6);
    place_led_spacer_mount_element(10, 5);
    place_led_spacer_mount_element(13, -2);
    place_led_spacer_mount_element(15, 6);
    place_led_spacer_mount_element(20, 4);
}

module place_led_spacer_mount(x_pos = 0, y_pos = 0) {
    if((x_pos % 2) == 0) {
        // even column
        translate([x_pos*dx_even_factor, y_pos*dy_even_factor, -5])
        led_spacer_mount();
    }
    else {
        // odd column
        translate([x_pos*dx_odd_factor, (2*y_pos-1)*dy_odd_factor, -5])
        led_spacer_mount();
    }
}

*translate([0, 0, 20])
plain_display_cover();

*plain_display_cover_cut();

*translate([0, 0, -20])
place_display_m3_mount_cut();

*display_clock_cover();
display_backlight_cover();
*led_spacer(0);
*place_led_spacer_mount();

*place_led_spacer();
